katetriestocode/catboard/illustrator/bolder.png

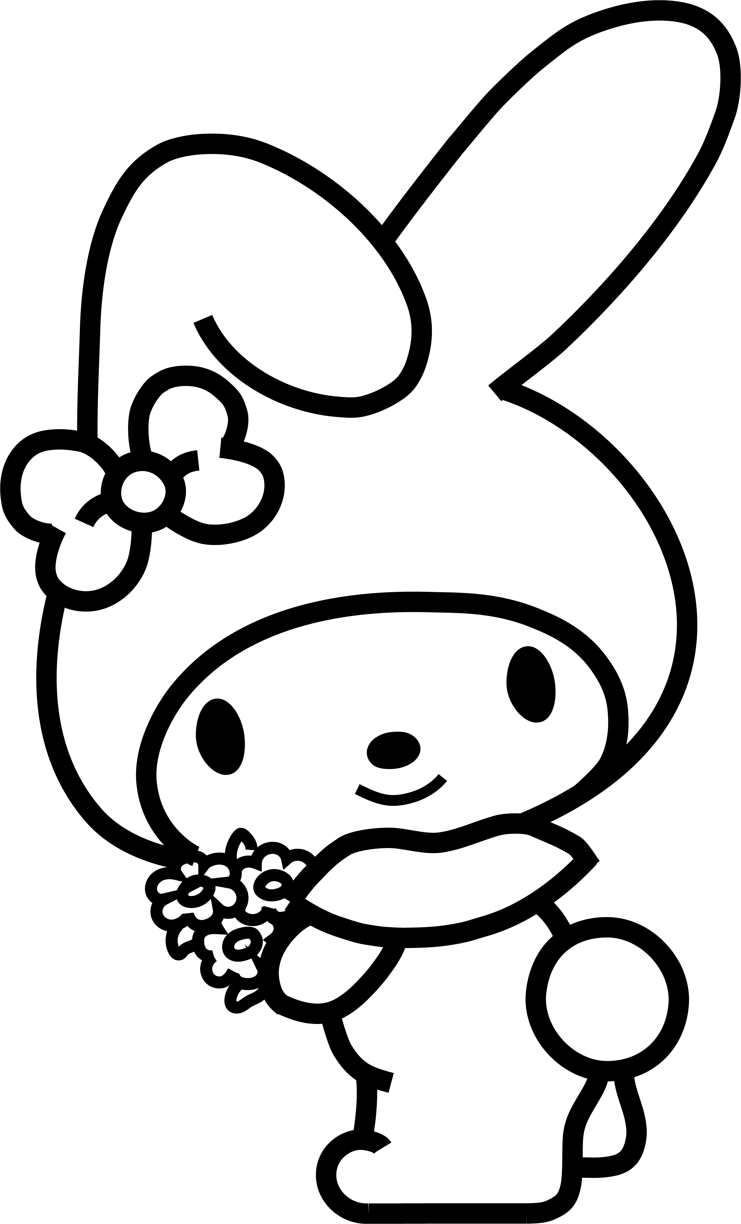
illustrator/bolder.png
